nrwiersma/aura-mon/firmware/src/data_log.cpp

//
// Created by Nicholas Wiersma on 2025/10/23.
//

#ifndef UNIT_TEST
#include "auramon.h"
#else
#include "../test/stubs/TestCore.h"
#include "data_log.h"
#endif

bool DataLog::begin() {
    if (_file) return true;

    mutex_enter_blocking(&sdMu);
    if (!sd.exists(DATA_LOG_PATH)) {
        String msgDir = DATA_LOG_PATH;
        msgDir.remove(msgDir.indexOf('/', 1));
        sd.mkdir(msgDir.c_str());
    }
    _file = sd.open(DATA_LOG_PATH, O_RDWR | O_CREAT);
    if (!_file) {
        mutex_exit(&sdMu);
        return false;
    }

    _fileSize = _file.size();
    _maxFileSize = max(_fileSize, _maxFileSize);
    if (_fileSize) {
        _first = readKey(0);
        _last = readKey(_fileSize - _recordSize);
        _entries = _fileSize / _recordSize;

        LOGD("Found %d entries in log file", _entries);
    }

    if (_first.ts > _last.ts) {
        _wrapPos = findWrapPos(0, _first.ts, _fileSize - _recordSize, _last.ts);
        _file.seek(_wrapPos);
        _file.read(&_first, sizeof(LogRecordKey));
        _file.seek(_wrapPos - _recordSize);
        _file.read(&_last, sizeof(LogRecordKey));
    }

    if (_fileSize && _last.rev - _first.rev + 1 != _entries) {
        _file.close();
        sd.remove(DATA_LOG_PATH);
        mutex_exit(&sdMu);

        LOGE("log: File %s damaged.\r\n", DATA_LOG_PATH);
        LOGE("log: Deleting %s and restarting.\r\n", DATA_LOG_PATH);

        mutex_enter_blocking(&sdMu);

        rp2040.reboot();
    }

    mutex_exit(&sdMu);
    return true;
}

void DataLog::end() {
    mutex_enter_blocking(&_mu);
    if (_file) {
        mutex_enter_blocking(&sdMu);
        _file.close();
        mutex_exit(&sdMu);
    }
    mutex_exit(&_mu);
}

uint32_t DataLog::entries() {
    mutex_enter_blocking(&_mu);
    auto e = _entries;
    mutex_exit(&_mu);
    return e;
}

uint32_t DataLog::firstRev() {
    mutex_enter_blocking(&_mu);
    auto r = _first.rev;
    mutex_exit(&_mu);
    return r;
}

uint32_t DataLog::firstTS() {
    mutex_enter_blocking(&_mu);
    auto t = _first.ts;
    mutex_exit(&_mu);
    return t;
}

uint32_t DataLog::lastRev() {
    mutex_enter_blocking(&_mu);
    auto r = _last.rev;
    mutex_exit(&_mu);
    return r;
}

uint32_t DataLog::lastTS() {
    mutex_enter_blocking(&_mu);
    auto t = _last.ts;
    mutex_exit(&_mu);
    return t;
}

uint32_t DataLog::fileSize() {
    mutex_enter_blocking(&_mu);
    auto s = _fileSize;
    mutex_exit(&_mu);
    return s;
}

error DataLog::read(uint32_t ts, LogRecord *rec, uint32_t timeoutMS) {
    ts -= ts % _interval;

    if (timeoutMS > 0) {
        if (!mutex_enter_timeout_ms(&_mu, timeoutMS)) {
            return newError("mutex timeout");
        }
    } else {
        mutex_enter_blocking(&_mu);
    }

    if (!_file) {
        mutex_exit(&_mu);
        return newError("file not open");
    }

    if (_entries == 0) {
        mutex_exit(&_mu);
        return newError("no entries");
    }
    if (ts < _first.ts) {
        // Before the beginning of the file.
        readRev(_first.rev, rec);
        rec->ts = ts;

        mutex_exit(&_mu);
        return {};
    }
    if (ts > _last.ts) {
        // Past the end of the file.
        readRev(_last.rev, rec);
        rec->ts = ts;

        mutex_exit(&_mu);
        return {};
    }

    // Check the last records cache if we are in the time range.
    if (ts >= _last.ts - _lastCacheSize * _interval) {
        for (int i = 0; i < _lastCacheSize; i++) {
            uint32_t cacheTS = _lastCache[i].ts;
            if (cacheTS == ts) {
                rp2040.memcpyDMA(rec, &_lastCache[i], sizeof(LogRecord));

                metrics.datalog_cache_hit.fetch_add(1, std::memory_order_relaxed);

                mutex_exit(&_mu);
                return {};
            }
        }
    }

    // Check the last read record cache, it is likely that reads will be sequential, so this will give us a good hint
    // of where to search.
    if (_lastReadTS < ts) {
        uint32_t rev = (ts - _lastReadTS) / _interval + _lastReadRev;
        readRev(rev, rec);
        if (rec->ts == ts) {
            mutex_exit(&_mu);
            return {};
        }
    }

    uint32_t lowRev = _first.rev;
    uint32_t lowTS = _first.ts;
    uint32_t highRev = _last.rev;
    uint32_t highTS = _last.ts;

    search(ts, rec, lowTS, lowRev, highTS, highRev);
    rec->ts = ts;

    mutex_exit(&_mu);
    return {};
}

error DataLog::write(LogRecord *rec) {
    if (!mutex_enter_timeout_ms(&_mu, 100)) {
        return newError("mutex timeout");
    }

    if (!_file) {
        mutex_exit(&_mu);
        return newError("file not open");
    }
    if (rec->ts <= _last.ts) {
        mutex_exit(&_mu);
        return newError("timestamp not increasing");
    }
    rec->rev = ++_last.rev;
    _last.ts = rec->ts;

    // Add it to the last records cache.
    _lastCache[_lastCachePos++] = *rec;
    _lastCachePos %= _lastCacheSize;

    if (_wrapPos || _fileSize >= _maxFileSize) {
        // The file has/should wrap.
        if (!mutex_enter_timeout_ms(&sdMu, 100)) {
            mutex_exit(&_mu);
            return newError("sd card mutex timeout");
        }
        _file.seek(_wrapPos);
        _wrapPos = (_wrapPos + _recordSize) % _fileSize;
        _file.write(rec, _recordSize);
        _file.flush();
        _file.seek(_wrapPos);

        // Read the new first key.
        auto key = LogRecordKey{};
        _file.read(&key, sizeof(LogRecordKey));
        _first = key;
        mutex_exit(&sdMu);

        metrics.datalog_write_io.fetch_add(1, std::memory_order_relaxed);

        mutex_exit(&_mu);
        return {};
    }

    // No wrap, just write at the end of the file.
    if (!mutex_enter_timeout_ms(&sdMu, 100)) {
        mutex_exit(&_mu);
        return newError("sd card mutex timeout");
    }
    _file.seek(_fileSize);
    _file.write(rec, _recordSize);
    _file.flush();
    mutex_exit(&sdMu);

    _fileSize += _recordSize;
    _entries++;

    // If this is the first record, set the first timestamp and rev.
    if (_entries == 1) {
        _first.ts = rec->ts;
        _first.rev = rec->rev;
    }
    metrics.datalog_write_io.fetch_add(1, std::memory_order_relaxed);

    mutex_exit(&_mu);
    return {};
}

DataLog::LogRecordKey DataLog::readKey(uint32_t pos) {
    auto key = LogRecordKey{};
    _file.seek(pos);
    _file.read(&key, sizeof(LogRecordKey));

    metrics.datalog_read_io.fetch_add(1, std::memory_order_relaxed);

    return key;
}

uint8_t DataLog::readRev(uint32_t rev, LogRecord *rec) {
    if (rev < _first.rev || rev > _last.rev) {
        return 1;
    }

    uint32_t pos = ((rev - _first.rev) * _recordSize + _wrapPos) % _fileSize;

    if (!mutex_enter_timeout_ms(&sdMu, 200)) {
        return 1;
    }
    _file.seek(pos);
    _file.read(rec, _recordSize);
    mutex_exit(&sdMu);

    _lastReadTS = rec->ts;
    _lastReadRev = rec->rev;

    metrics.datalog_read_io.fetch_add(1, std::memory_order_relaxed);

    return 0;
}

void DataLog::search(const uint32_t ts, LogRecord *        rec,
                     const uint32_t lowTS, const uint32_t  lowRev,
                     const uint32_t highTS, const uint32_t highRev) {
    if (highRev - lowRev <= 1) {
        readRev(lowRev, rec);
        return;
    }
    readRev((lowRev + highRev) / 2, rec);
    if (rec->ts == ts) {
        return;
    }
    if (rec->ts < ts) {
        search(ts, rec, rec->ts, rec->rev, highTS, highRev);
        return;
    }
    search(ts, rec, lowTS, lowRev, rec->ts, rec->rev);
}

uint32_t DataLog::findWrapPos(const uint32_t lowPos, const uint32_t lowTS, const uint32_t highPos,
                              const uint32_t highTS) {
    if (highPos - lowPos == _recordSize) {
        return highPos;
    }
    uint32_t midPos = (lowPos + highPos) / 2;
    midPos += midPos % _recordSize;

    uint32_t midTS = readKey(midPos).ts;
    if (midTS > lowTS) {
        return findWrapPos(midPos, midTS, highPos, highTS);
    }
    return findWrapPos(lowPos, lowTS, midPos, midTS);
}
