nrwiersma/aura-mon/firmware/src/sync_devices.cpp

//
// Created by Nicholas Wiersma on 2026/01/25.
//

#ifndef UNIT_TEST
#include "auramon.h"
#else
#include "../test/stubs/TestCore.h"
#endif

void syncDeviceInfo() {
    for (uint32_t i = 0; i < MAX_DEVICES; i++) {
        if (deviceInfos[i] == nullptr) {
            if (devices[i] == nullptr) {
                continue;
            }

            // Remove device
            delete devices[i];
            devices[i] = nullptr;
            continue;
        }

        if (deviceInfos[i] != nullptr) {
            if (devices[i] == nullptr) {
                devices[i] = new InputDevice(deviceInfos[i]->addr);
            }
            devices[i]->enabled = deviceInfos[i]->enabled;
            devices[i]->name = deviceInfos[i]->name;
            devices[i]->calibration = deviceInfos[i]->calibration;
            devices[i]->reversed = deviceInfos[i]->reversed;
        }
    }
}

void syncDeviceAction() {
    if (deviceActionControl.type == DeviceActionType::None) {
        return;
    }

    deviceActionData = deviceActionControl;
    deviceActionControl = {DeviceActionType::None, 0};
}

void syncDeviceData() {
    for (uint32_t i = 0; i < MAX_DEVICES; i++) {
        if (devices[i] == nullptr) {
            if (deviceData[i] != nullptr) {
                delete deviceData[i];
                deviceData[i] = nullptr;
            }
            continue;
        }

        if (deviceData[i] == nullptr) {
            deviceData[i] = new InputDeviceData{};
        }

        deviceData[i]->name = devices[i]->name;
        deviceData[i]->volts = devices[i]->current.volts;
        deviceData[i]->amps = devices[i]->current.volts != 0.0
                                  ? (devices[i]->current.va / devices[i]->current.volts)
                                  : 0.0;
        deviceData[i]->pf = devices[i]->current.va != 0.0 ? devices[i]->current.watts / devices[i]->current.va : 0.0;
        deviceData[i]->hz = devices[i]->current.hz;
    }
}

uint32_t syncDevices(void *param) {
    (void) param;

    if (!mutex_enter_timeout_ms(&deviceInfoMu, 100)) {
        LOGE("syncDevices: could not acquire deviceInfoMu");
        return 50;
    }
    if (devicesChanged) {
        syncDeviceInfo();

        // Reset the changed flag.
        devicesChanged = false;
    }

    mutex_exit(&deviceInfoMu);

    if (!mutex_enter_timeout_ms(&deviceActionMu, 100)) {
        LOGE("syncDevices: could not acquire deviceActionMu");
        return 50;
    }

    syncDeviceAction();

    mutex_exit(&deviceActionMu);

    if (!mutex_enter_timeout_ms(&deviceDataMu, 100)) {
        LOGE("syncDevices: could not acquire deviceDataMu");
        return 50;
    }

    syncDeviceData();

    mutex_exit(&deviceDataMu);

    return 1000;
}
