nrwiersma/aura-mon/firmware/src/ethernet.h

//
// Created by Nicholas Wiersma on 2026/03/19.
//

#pragma once

struct NetworkConfig {
    String hostname;
    String ip;
    String gateway;
    String mask;
    String dns;

    NetworkConfig()
        : hostname("aura-mon"),
          ip(""),
          gateway(""),
          mask("255.255.255.0"),
          dns("8.8.8.8") {
    }

    bool hasIP() { return (!ip.isEmpty()); }
};
